FREILab/3DPrinter_Octoprint_Matrix_Display/Software/RemainingTimeDisplay/secret.h

// Printer Configutation
#define CONFIG_NAME "My printer name" 	// Printer display name
#define CONFIG_IP  	"192.168.1.99" 	// IP Adress of printer
#define CONFIG_PORT 80        		// Port of the printer

// Octoprint API key
#define SECRET_API "API_KEY"  // enter the API key here

// WiFi credentials
#define SECRET_SSID  "MY_SSID"          // your network SSID (name)
#define SECRET_PASS  "MY_WIFI_PASSWORD" // your network password
